braindefender/KLP-Lame-Keycaps/STEP/Choc Stem + Choc Size/90 deg Rotated/Choc_Stem_Choc_Size_Saddle_90deg.step

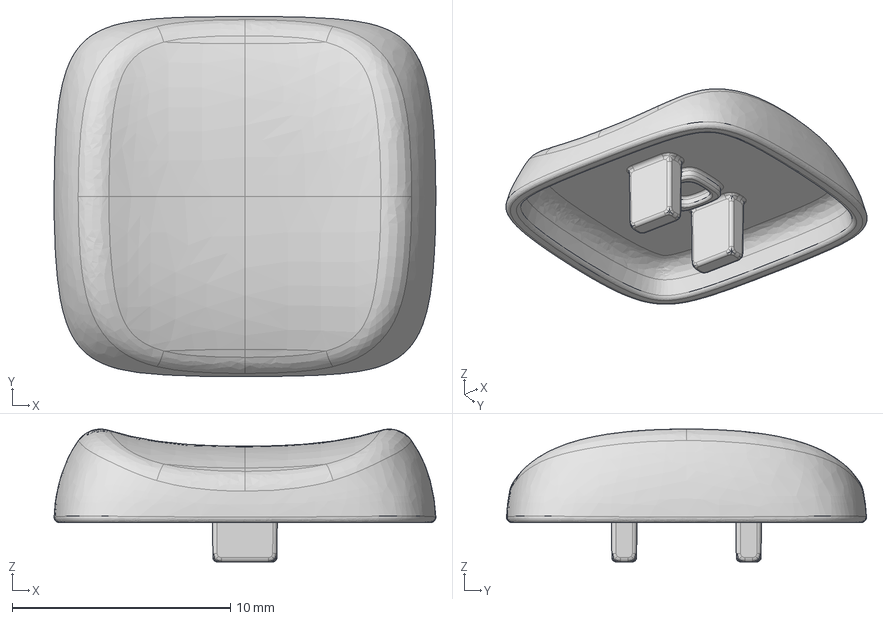
[picture p22: CAD file, 2025-07-13]
STEP/Choc Stem + Choc Size/90 deg Rotated/Choc_Stem_Choc_Size_Saddle_90deg.step
17.5 x 16.5 x 6.08 mm
