braindefender/KLP-Lame-Keycaps/STEP/MX Stem + Choc Size/MX_Stem_Choc_Size_1.5U_Saddle_V.step

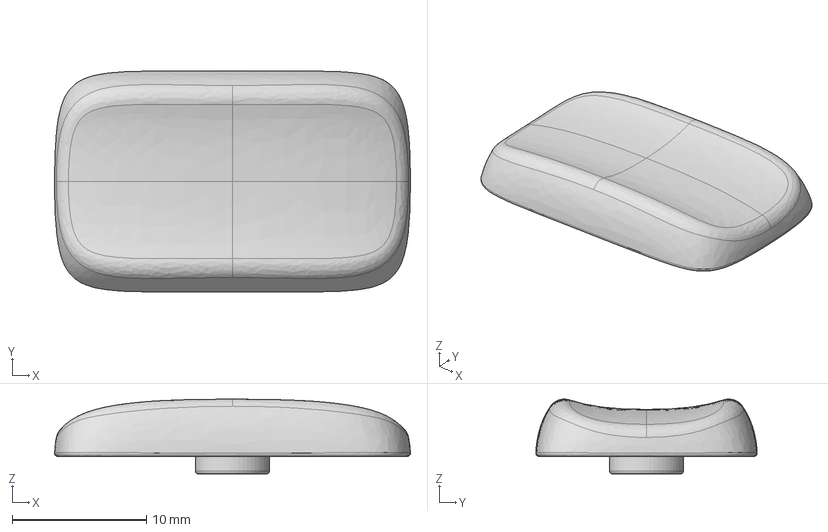
[picture p23: CAD file, 2025-11-16]
STEP/MX Stem + Choc Size/MX_Stem_Choc_Size_1.5U_Saddle_V.step
26.5 x 16.5 x 5.57 mm
