braindefender/KLP-Lame-Keycaps/STEP/MX Stem + MX Size/MX_Stem_MX_Size_1.5U_Saddle_V.step

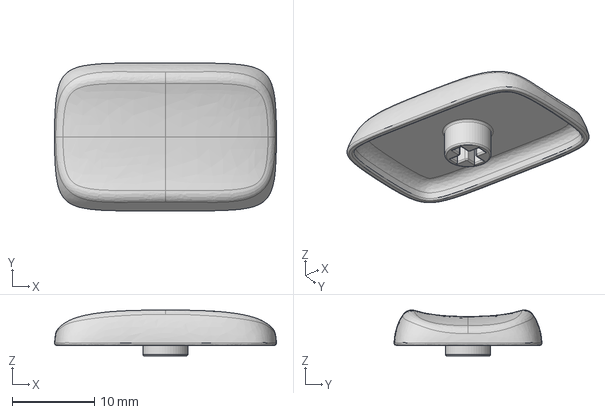
[picture p24: CAD file, 2025-11-16]
STEP/MX Stem + MX Size/MX_Stem_MX_Size_1.5U_Saddle_V.step
27.0 x 18.0 x 5.59 mm
