braindefender/KLP-Lame-Keycaps/STEP/Choc Stem + MX Size/90 deg Rotated/Choc_Stem_MX_Size_Normal_90deg.step

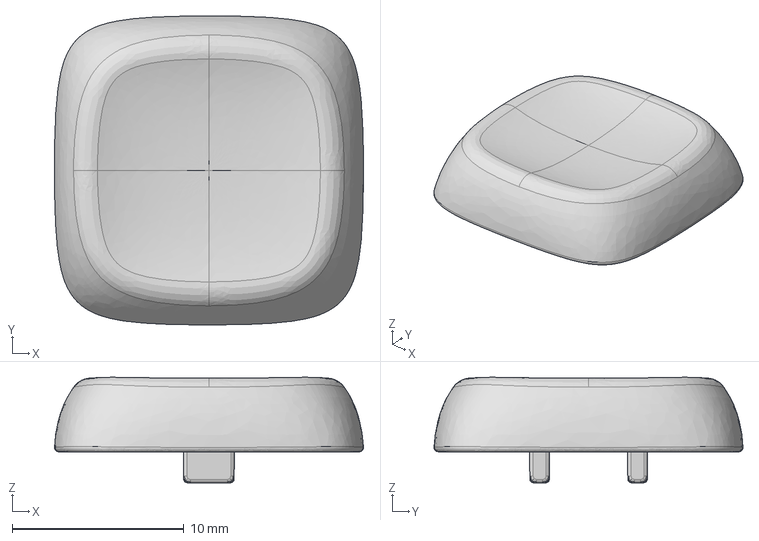
[picture p26: CAD file, 2025-07-13]
STEP/Choc Stem + MX Size/90 deg Rotated/Choc_Stem_MX_Size_Normal_90deg.step
18.0 x 18.0 x 6.14 mm
