braindefender/KLP-Lame-Keycaps/STEP/Choc Stem + MX Size/Choc_Stem_MX_Size_1.5U_Saddle_H.step

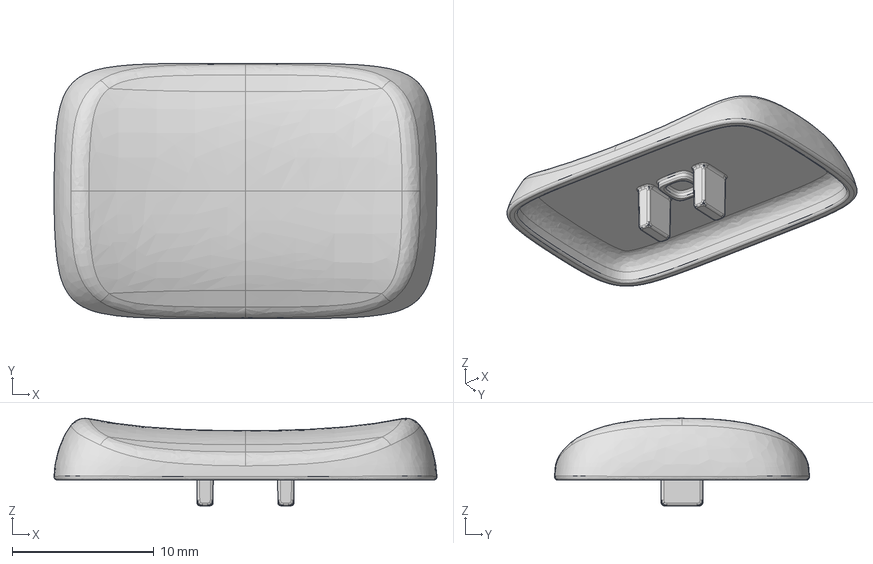
[picture p27: CAD file, 2025-11-16]
STEP/Choc Stem + MX Size/Choc_Stem_MX_Size_1.5U_Saddle_H.step
27.0 x 18.0 x 6.17 mm
