braindefender/KLP-Lame-Keycaps/STEP/MX Stem + MX Size/MX_Stem_MX_Size_Thumb.step

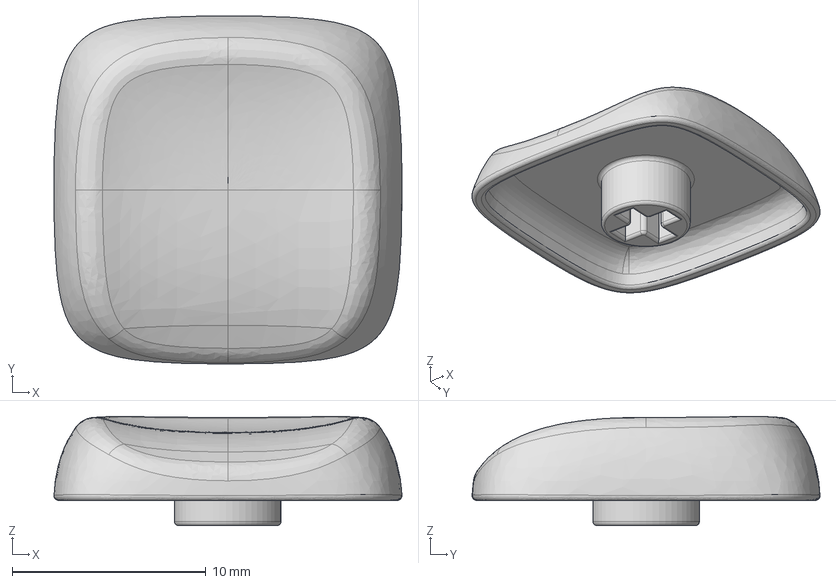
[picture p30: CAD file, 2025-01-18]
STEP/MX Stem + MX Size/MX_Stem_MX_Size_Thumb.step
18.0 x 18.0 x 5.64 mm
