braindefender/KLP-Lame-Keycaps/STEP/Choc Stem + Choc Size/90 deg Rotated/Choc_Stem_Choc_Size_Normal_Tilted_90deg.step

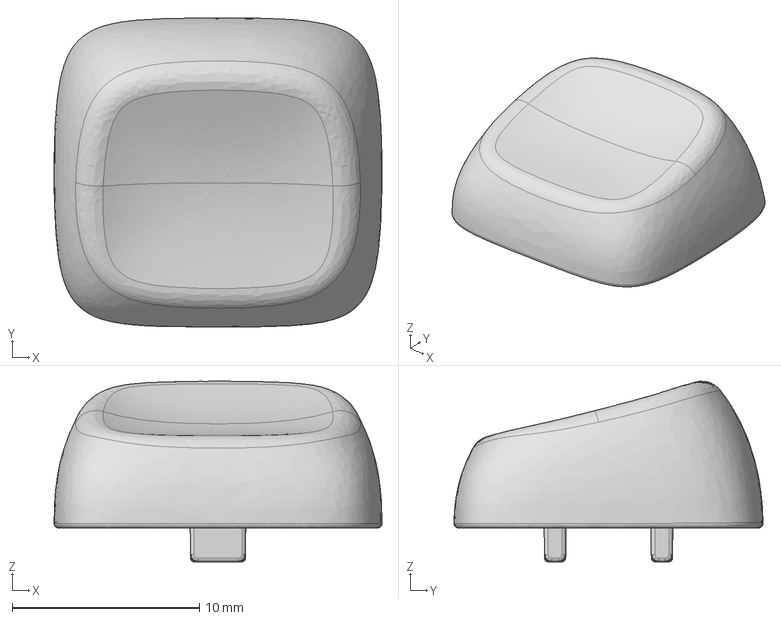
[picture p31: CAD file, 2025-07-13]
STEP/Choc Stem + Choc Size/90 deg Rotated/Choc_Stem_Choc_Size_Normal_Tilted_90deg.step
17.5 x 16.5 x 9.64 mm
