braindefender/KLP-Lame-Keycaps/STEP/MX Stem + Choc Size/MX_Stem_Choc_Size_Saddle_Homing.step

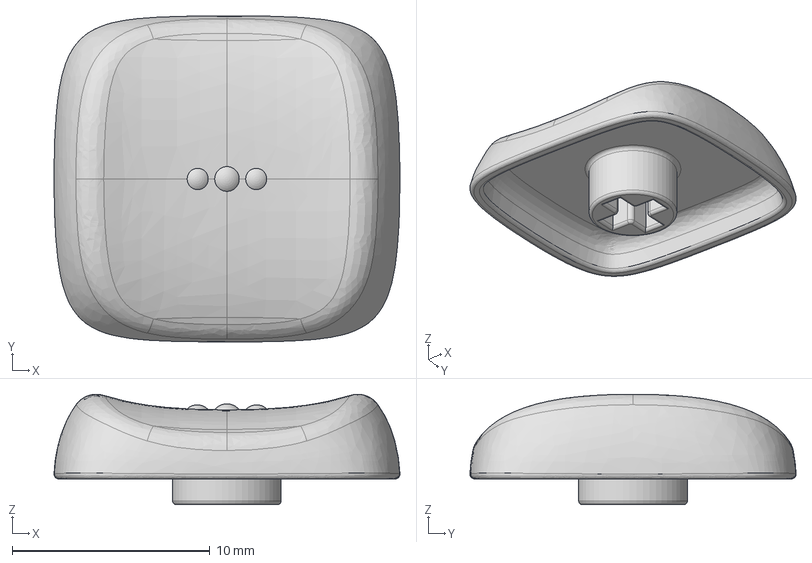
[picture p32: CAD file, 2025-05-10]
STEP/MX Stem + Choc Size/MX_Stem_Choc_Size_Saddle_Homing.step
17.5 x 16.5 x 5.58 mm
