braindefender/KLP-Lame-Keycaps/STEP/MX Stem + MX Size/MX_Stem_MX_Size_Normal_Homing.step

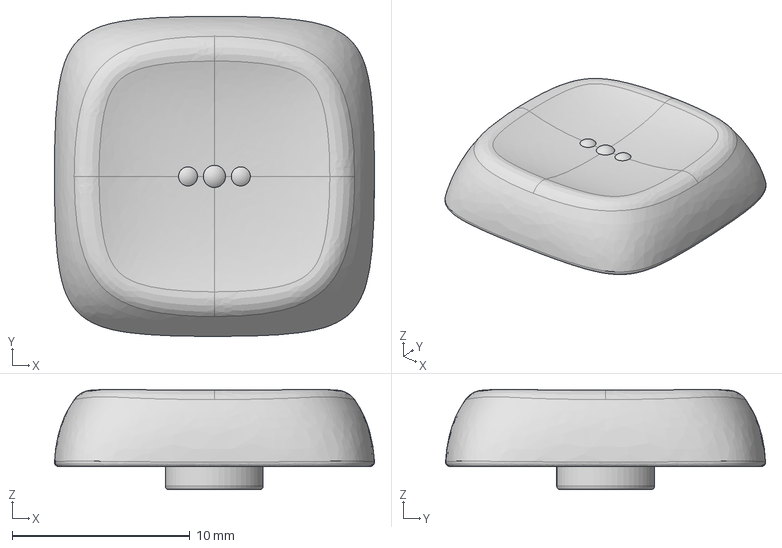
[picture p33: CAD file, 2025-01-18]
STEP/MX Stem + MX Size/MX_Stem_MX_Size_Normal_Homing.step
18.0 x 18.0 x 5.64 mm
