braindefender/KLP-Lame-Keycaps/STEP/MX Stem + Choc Size/MX_Stem_Choc_Size_Saddle_Tilted.step

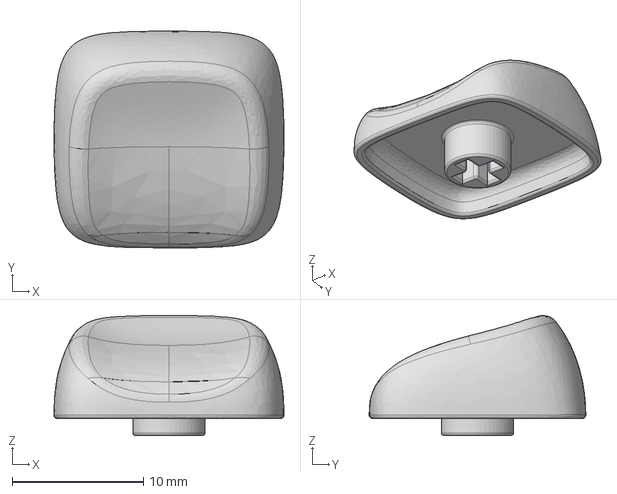
[picture p34: CAD file, 2025-05-10]
STEP/MX Stem + Choc Size/MX_Stem_Choc_Size_Saddle_Tilted.step
17.5 x 16.5 x 9.13 mm
