braindefender/KLP-Lame-Keycaps/STEP/MX Stem + MX Size/MX_Stem_MX_Size_Saddle.step

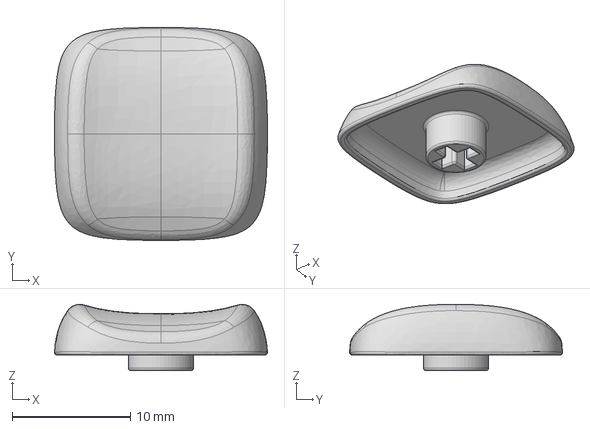
[picture p35: CAD file, 2025-01-18]
STEP/MX Stem + MX Size/MX_Stem_MX_Size_Saddle.step
18.0 x 18.0 x 5.59 mm
