braindefender/KLP-Lame-Keycaps/STEP/MX Stem + Choc Size/MX_Stem_Choc_Size_Normal.step

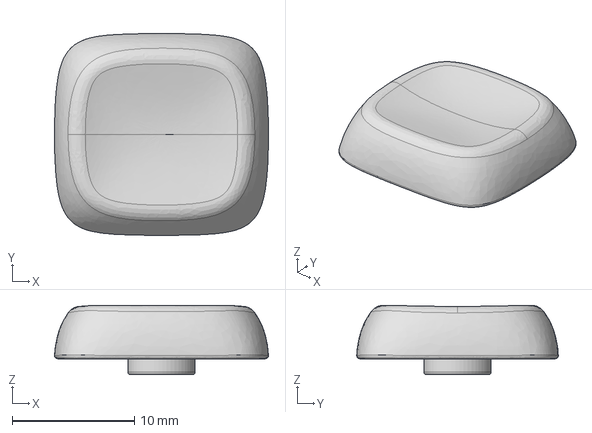
[picture p36: CAD file, 2025-05-10]
STEP/MX Stem + Choc Size/MX_Stem_Choc_Size_Normal.step
17.5 x 16.5 x 5.67 mm
