braindefender/KLP-Lame-Keycaps/STEP/MX Stem + MX Size/MX_Stem_MX_Size_Normal_Tilted.step

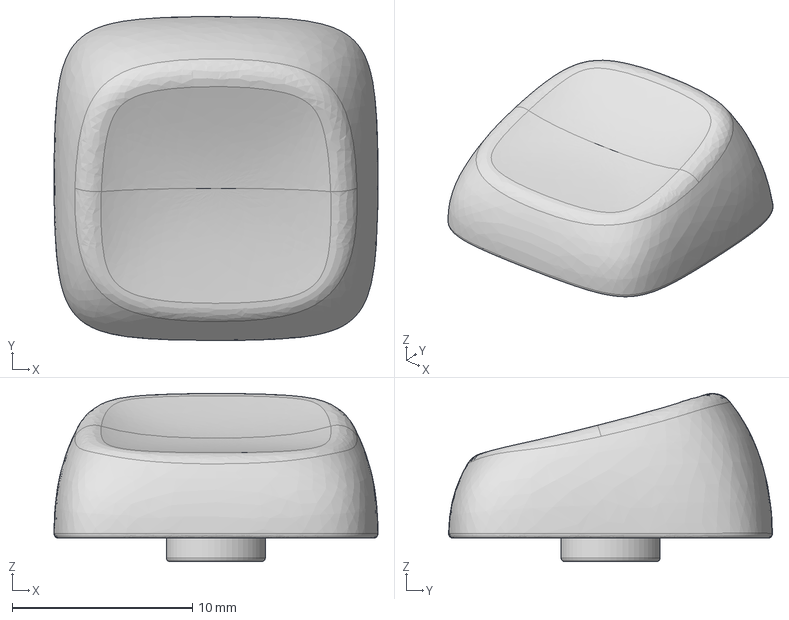
[picture p37: CAD file, 2025-01-18]
STEP/MX Stem + MX Size/MX_Stem_MX_Size_Normal_Tilted.step
18.0 x 18.0 x 9.34 mm
