braindefender/KLP-Lame-Keycaps/STEP/MX Stem + MX Size/MX_Stem_MX_Size_Saddle_Tilted.step

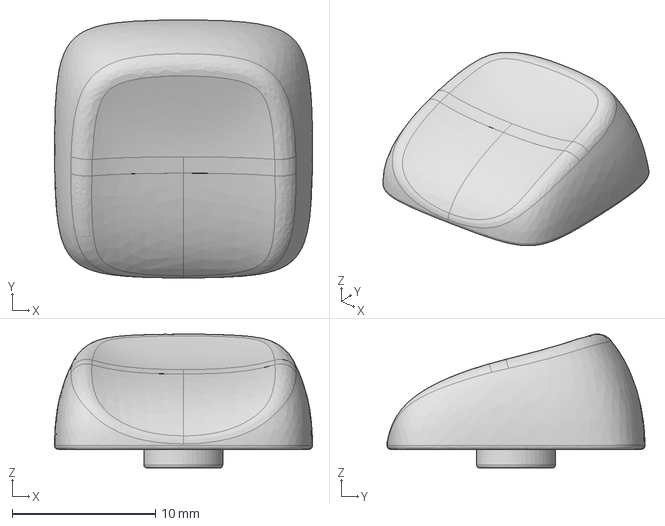
[picture p38: CAD file, 2025-01-18]
STEP/MX Stem + MX Size/MX_Stem_MX_Size_Saddle_Tilted.step
18.0 x 18.0 x 9.34 mm
