braindefender/KLP-Lame-Keycaps/STEP/MX Stem + Choc Size/MX_Stem_Choc_Size_Thumb.step

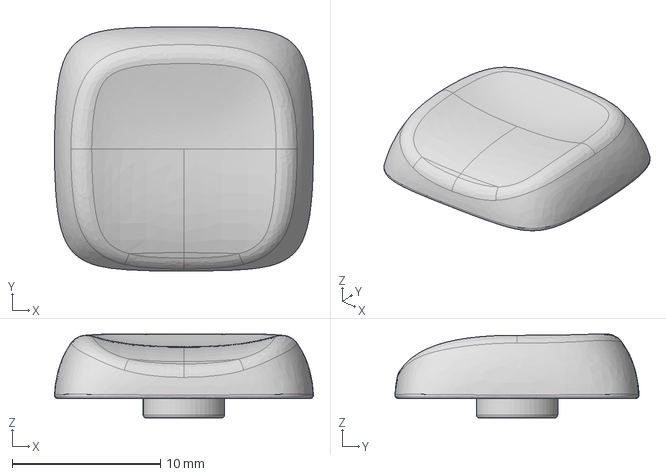
[picture p39: CAD file, 2025-05-10]
STEP/MX Stem + Choc Size/MX_Stem_Choc_Size_Thumb.step
17.5 x 16.5 x 5.67 mm
